tomduf/printer3d/travail/Support clipsable.JPG

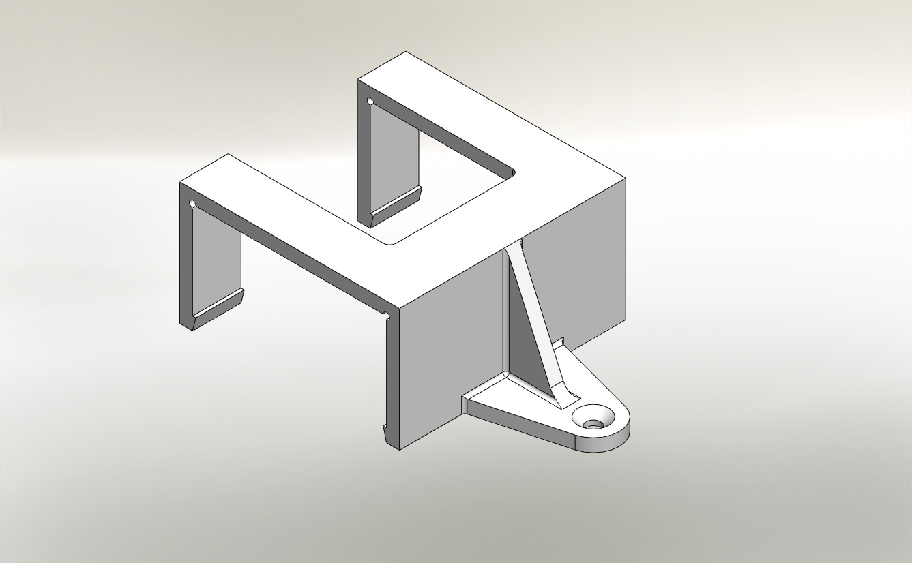
travail/Support clipsable.JPG
