tomduf/printer3d/travail/slices-ocot-10/layer_0000(z=0.000).png

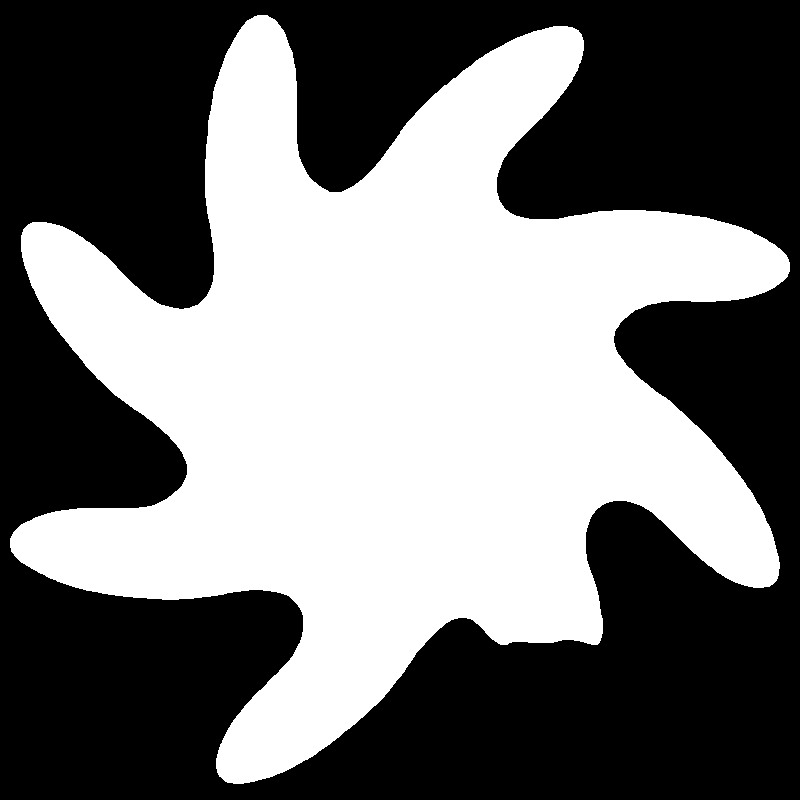
travail/slices-ocot-10/layer_0000(z=0.000).png
