tomduf/printer3d/travail/slices-ocot-10/layer_0005(z=5.001).png

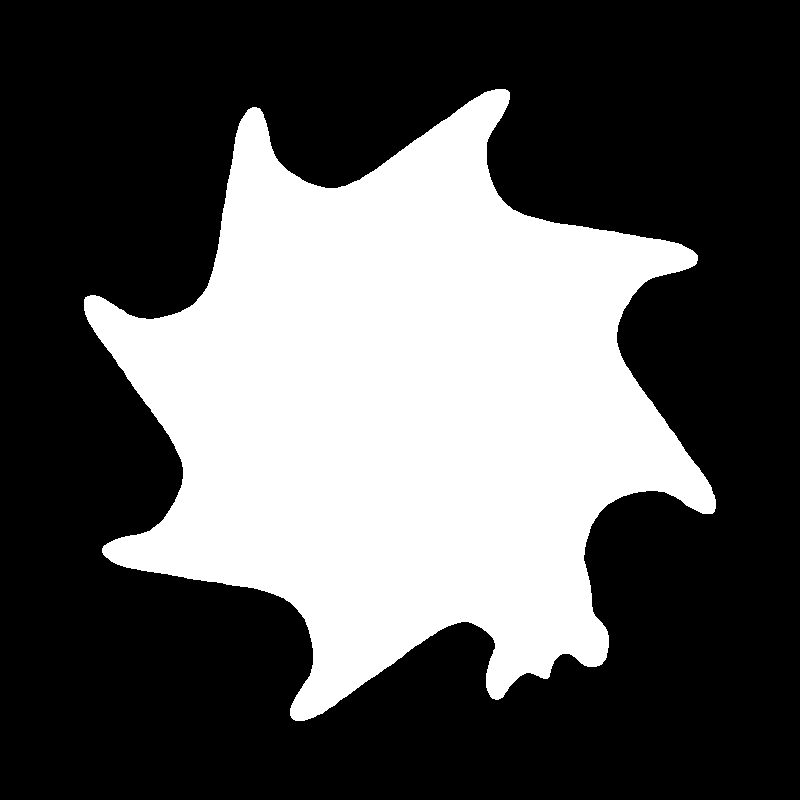
travail/slices-ocot-10/layer_0005(z=5.001).png
