tomduf/printer3d/travail/slices-ocot-10/layer_0006(z=6.000).png

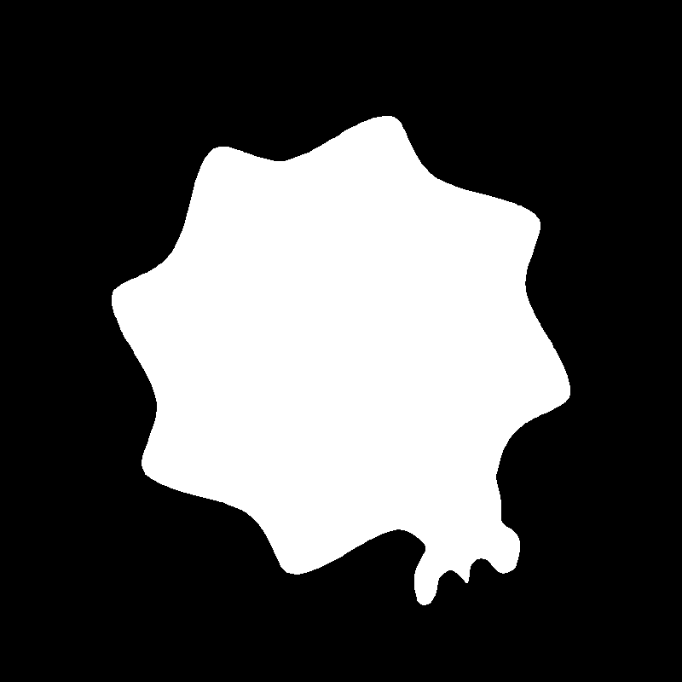
travail/slices-ocot-10/layer_0006(z=6.000).png
