tomduf/printer3d/travail/slices-ocot-10/layer_0009(z=9.000).png

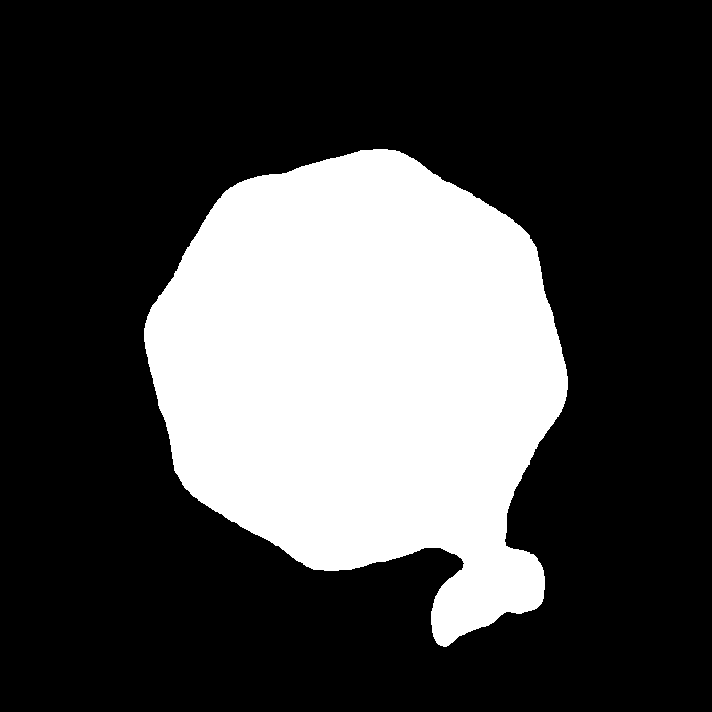
travail/slices-ocot-10/layer_0009(z=9.000).png
