tomduf/printer3d/travail/slices-octo-57/layer_0018(z=18.001).png

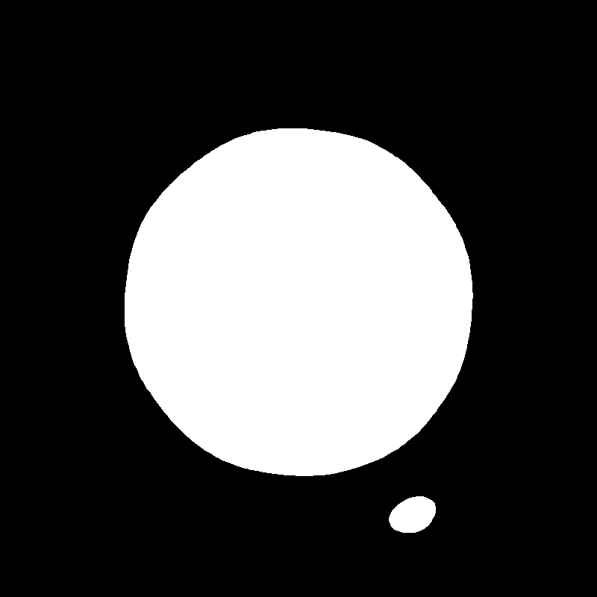
travail/slices-octo-57/layer_0018(z=18.001).png
