tomduf/printer3d/travail/slices-octo-57/layer_0023(z=23.000).png

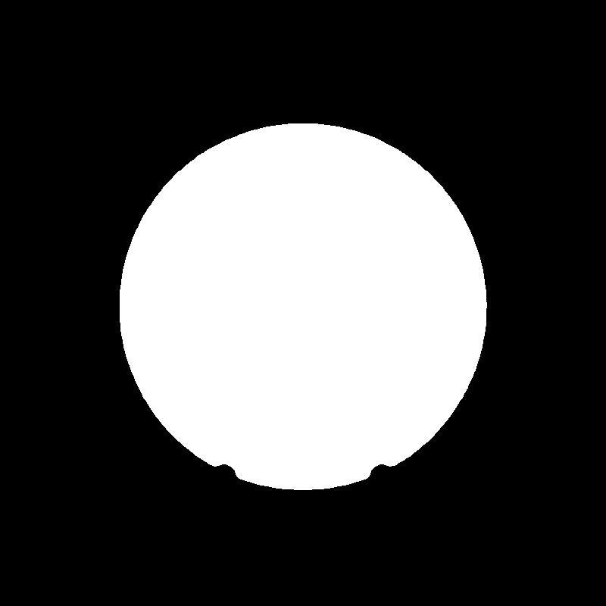
travail/slices-octo-57/layer_0023(z=23.000).png
