tomduf/printer3d/travail/slices-octo-57/layer_0029(z=29.000).png

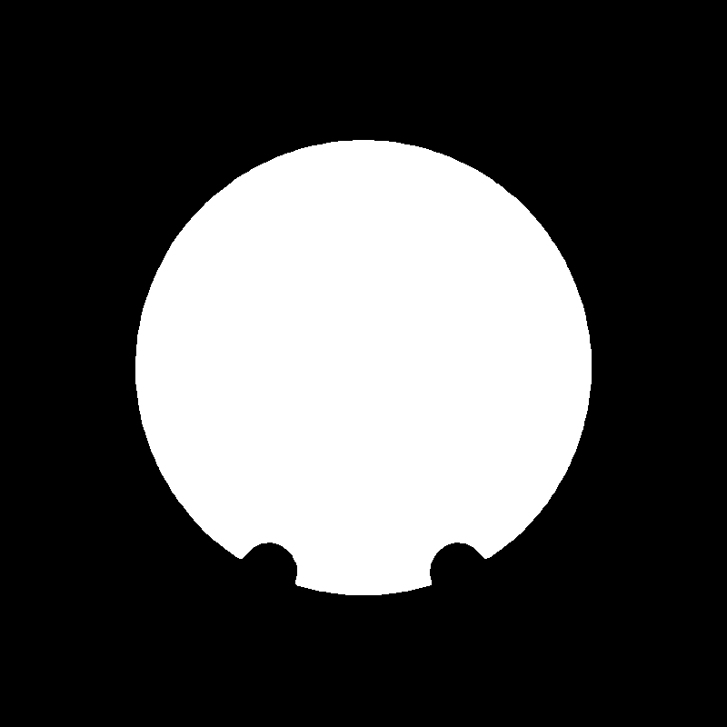
travail/slices-octo-57/layer_0029(z=29.000).png
