tomduf/printer3d/travail/slices-octo-57/layer_0046(z=46.001).png

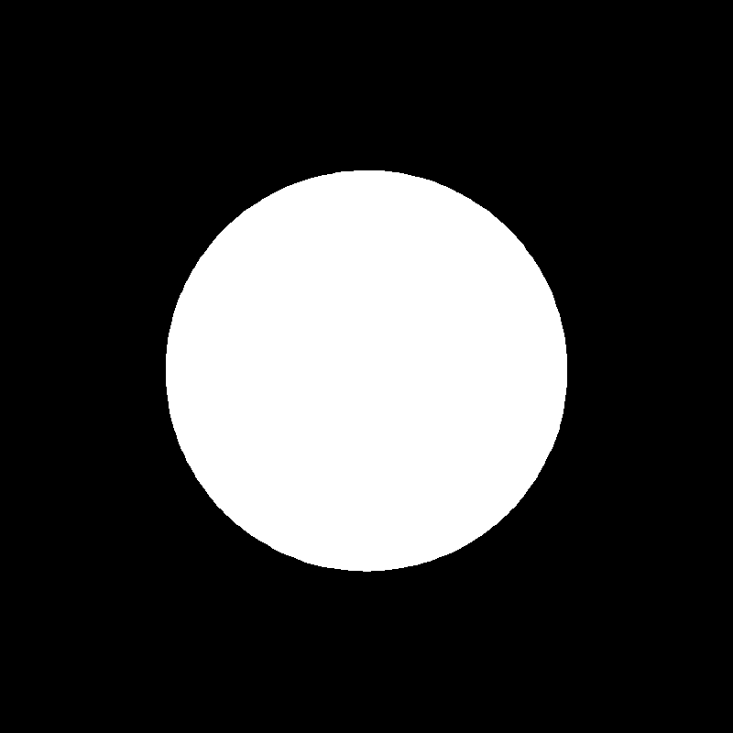
travail/slices-octo-57/layer_0046(z=46.001).png
