tomduf/printer3d/travail/slices-octo-57/layer_0050(z=50.000).png

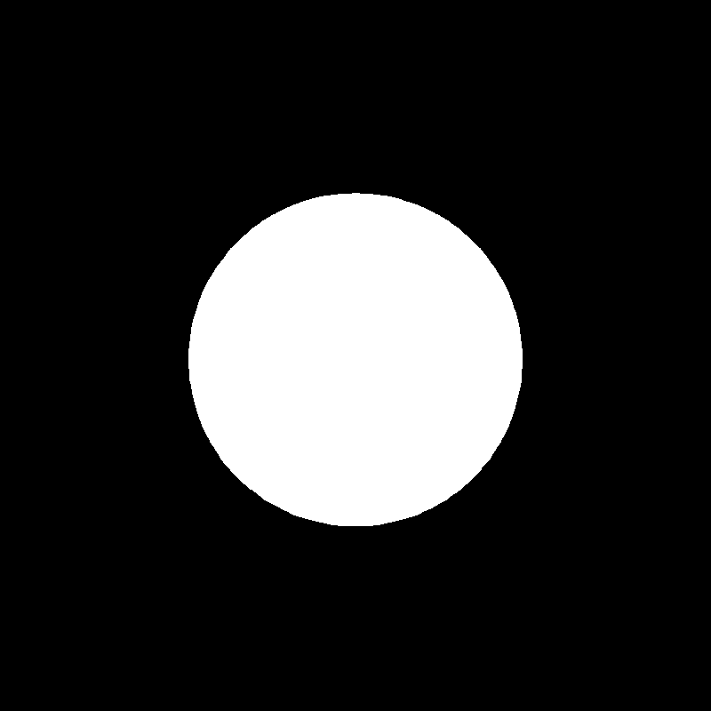
travail/slices-octo-57/layer_0050(z=50.000).png
