tomduf/printer3d/travail/slices-octo-57/layer_0053(z=53.000).png

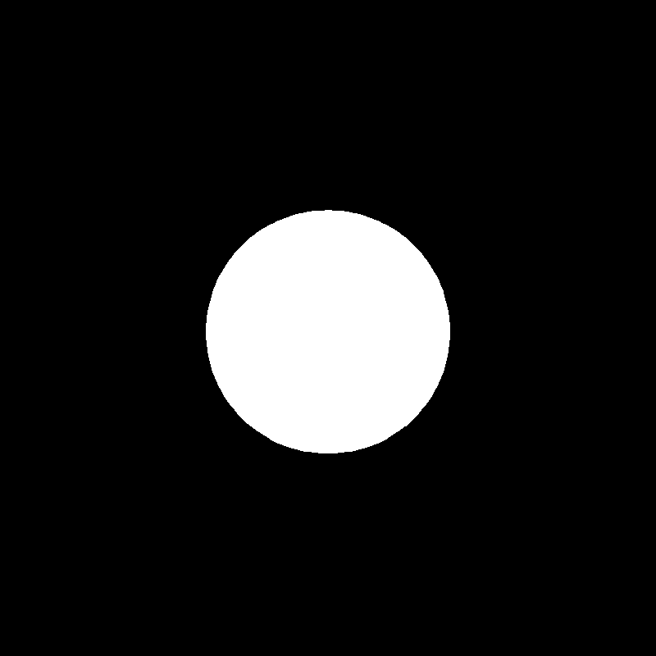
travail/slices-octo-57/layer_0053(z=53.000).png
