tomduf/printer3d/travail/slices-octo-57/layer_0055(z=55.000).png

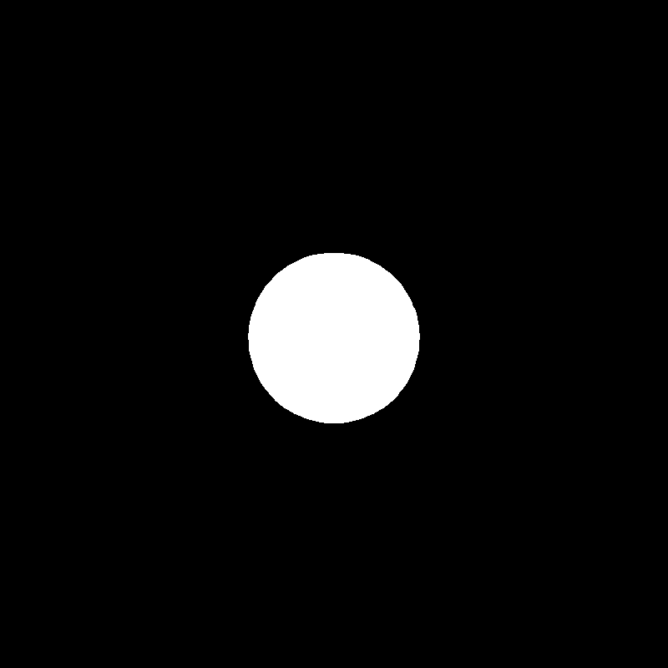
travail/slices-octo-57/layer_0055(z=55.000).png
