tomduf/printer3d/travail/solidworks/Rexroth-ecrou M4.SLDPRT

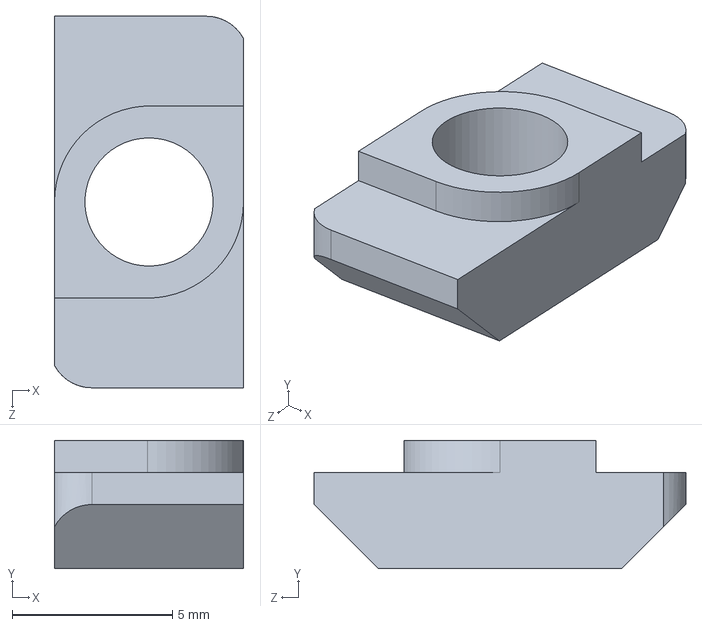
[picture p23: CAD file, 2014-04-27]
travail/solidworks/Rexroth-ecrou M4.SLDPRT
5.90 x 4.00 x 11.6 mm
